agkeck-iivi/internet_radio_v3/components/pcm5122_board/pcm5122_driver.h

#ifndef __PCM5122_H__
#define __PCM5122_H__

#include "audio_hal.h"
#include "driver/i2c.h"
#include "esp_types.h"

#ifdef __cplusplus
extern "C" {
#endif

#define PCM5122_ADDR 0x98 // 8-bit Write Address (7-bit 0x4C << 1)

// Selected PCM5122 Registers
#define PCM5122_PAGE 0x00
#define PCM5122_RESET 0x01
#define PCM5122_STANDBY 0x02
#define PCM5122_MUTE 0x03
#define PCM5122_PLL_EN 0x04
#define PCM5122_PLL_REF 0x0D
#define PCM5122_DAC_CLK_SRC 0x0E
#define PCM5122_ERROR_DETECT 0x25
#define PCM5122_I2S_CONFIG 0x28
#define PCM5122_VOL_L 0x3D
#define PCM5122_VOL_R 0x3E
#define PCM5122_DIGITAL_VOL_CTRL 0x3C
#define PCM5122_DIGITAL_VOL_RAMP 0x3F
#define PCM5122_AUTO_MUTE 0x41
#define PCM5122_ANALOG_GAIN_L 0x6C
#define PCM5122_ANALOG_GAIN_R 0x6D
#define PCM5122_POWER_STATE 0x76

#define PCM5122_PLL_REF_BCK 0x10
#define PCM5122_DAC_CLK_PLL 0x10

// Digital Volume Ramp Control (Reg 63)
// Frequency: 00=every sample, 01=2nd, 10=4th, 11=8th
// Step: 00=0.5dB, 01=1dB, 10=2dB, 11=4dB
#define PCM5122_RAMP_FREQ_1FS 0x00
#define PCM5122_RAMP_FREQ_2FS 0x01
#define PCM5122_RAMP_FREQ_4FS 0x02
#define PCM5122_RAMP_FREQ_8FS 0x03

#define PCM5122_RAMP_STEP_0_5DB 0x00
#define PCM5122_RAMP_STEP_1DB 0x01
#define PCM5122_RAMP_STEP_2DB 0x02
#define PCM5122_RAMP_STEP_4DB 0x03

// Macros to build the Reg 63 value
#define PCM5122_RAMP_UP_CONFIG(freq, step) (((freq) << 6) | ((step) << 4))
#define PCM5122_RAMP_DN_CONFIG(freq, step) (((freq) << 2) | ((step) << 0))

esp_err_t pcm5122_init(audio_hal_codec_config_t *cfg);
esp_err_t pcm5122_deinit(void);

esp_err_t pcm5122_ctrl_state(audio_hal_codec_mode_t mode,
                             audio_hal_ctrl_t ctrl_state);
esp_err_t pcm5122_config_i2s(audio_hal_codec_mode_t mode,
                             audio_hal_codec_i2s_iface_t *iface);

esp_err_t pcm5122_set_voice_volume(int volume);
esp_err_t pcm5122_get_voice_volume(int *volume);
esp_err_t pcm5122_apply_analog_attenuation(void);

esp_err_t pcm5122_set_mute(bool enable);
esp_err_t pcm5122_get_mute(bool *mute);

esp_err_t pcm5122_set_ramp_rate(uint8_t config_val);

esp_err_t pcm5122_pa_power(bool enable);

#ifdef __cplusplus
}
#endif

#endif //__PCM5122_H__
