agkeck-iivi/internet_radio_v3/main/audio_pipeline_manager.c

#include "audio_pipeline_manager.h"
#include "aac_decoder.h"
#include "app_config.h"
#include "audio_common.h"
#include "audio_event_iface.h"
#include "board.h" // For CONFIG_ESP32_C3_LYRA_V2_BOARD and I2S_STREAM_PDM_TX_CFG_DEFAULT
#include "driver/gpio.h"
#include "esp_log.h"
#include "esp_sleep.h"
#include "esp_task_wdt.h"
#include "flac_decoder.h"
#include "http_stream.h"
#include "i2s_stream.h"
#include "internet_radio_adf.h"
#include "ir_remote.h"
#include "lvgl_ssd1306_setup.h"
#include "mp3_decoder.h"
#include "ogg_decoder.h"
#include "sdkconfig.h"
#include <string.h>

extern audio_pipeline_components_t audio_pipeline_components;
extern volatile bool g_is_pipeline_running;

static const char *TAG = "AUDIO_PIPELINE_MGR";
volatile uint64_t g_bytes_read = 0;

const char *codec_type_to_string(codec_type_t codec) {
  switch (codec) {
  case CODEC_TYPE_MP3:
    return "MP3";
  case CODEC_TYPE_AAC:
    return "AAC";
  case CODEC_TYPE_OGG:
    return "OGG";
  case CODEC_TYPE_FLAC:
    return "FLAC";
  default:
    return "Unknown Codec";
  }
}

void delayed_audio_on_task(void *pvParameters) {
  vTaskDelay(pdMS_TO_TICKS(200));
  ESP_ERROR_CHECK(ir_remote_turn_audio_on());
  vTaskDelete(NULL);
}

static int _http_stream_event_handle(http_stream_event_msg_t *msg) {
  switch (msg->event_id) {
  case HTTP_STREAM_RESOLVE_ALL_TRACKS:
    return ESP_OK;

  case HTTP_STREAM_FINISH_TRACK:
    return http_stream_next_track(msg->el);

  case HTTP_STREAM_FINISH_PLAYLIST:
    return http_stream_fetch_again(msg->el);

  case HTTP_STREAM_ON_RESPONSE:
    // This is called for each chunk of data received
    g_bytes_read += msg->buffer_len;
    // You could log it here, but it will be very verbose.
    // ESP_LOGI(TAG, "Bytes read: %llu", g_bytes_read);
    return ESP_OK;
  default:
    return ESP_OK;
  }
}

static esp_err_t codec_event_cb(audio_element_handle_t el,
                                audio_event_iface_msg_t *msg, void *ctx) {
  ESP_LOGI(TAG, "Codec event callback triggered for element: %s, command: %d",
           audio_element_get_tag(el), msg->cmd);
  if (msg->source_type == AUDIO_ELEMENT_TYPE_ELEMENT &&
      msg->source == (void *)el) {
    if (msg->cmd == AEL_MSG_CMD_REPORT_MUSIC_INFO) {
      audio_element_info_t music_info = {0};
      audio_element_getinfo(el, &music_info);
      ESP_LOGI(TAG,
               "[ * ] Callback: Receive music info from codec decoder, "
               "sample_rate=%d, bits=%d, ch=%d",
               music_info.sample_rates, music_info.bits, music_info.channels);
      ESP_ERROR_CHECK(i2s_stream_set_clk(
          audio_pipeline_components.i2s_stream_writer, music_info.sample_rates,
          music_info.bits, music_info.channels));

      extern bool get_mute_state(void);
      if (g_runtime_config.ir_protocol != IR_PROTOCOL_NONE) {
        ESP_LOGI(TAG, "Audio stream active. Ensuring Bose Audio is ON.");
        ir_remote_turn_audio_on();
        // send another ir command after a delay
        xTaskCreate(delayed_audio_on_task, "delayed_audio_on_task", 3*1024, NULL,
                    tskIDLE_PRIORITY + 1, NULL);
      }
    }
  }
  return ESP_OK;
}
esp_err_t create_audio_pipeline(audio_pipeline_components_t *components,
                                codec_type_t codec_type, const char *uri) {

  if (components == NULL) {
    ESP_LOGE(TAG, "audio_pipeline_components_t pointer is NULL");
    return ESP_ERR_INVALID_ARG;
  }
  if (uri == NULL) {
    ESP_LOGE(TAG, "URI is NULL");
    return ESP_ERR_INVALID_ARG;
  }
  // board works here
  esp_err_t ret = ESP_OK;

  ESP_LOGI(TAG, "Creating audio pipeline for codec type: %s with URI: %s",
           codec_type_to_string(codec_type), uri);

  // Save current state for recreation after wakeup
  components->current_codec = codec_type;
  strncpy(components->current_uri, uri, sizeof(components->current_uri) - 1);
  components->current_uri[sizeof(components->current_uri) - 1] = '\0';

  audio_pipeline_cfg_t pipeline_cfg = DEFAULT_AUDIO_PIPELINE_CONFIG();
  //   pipeline_cfg.rb_size = 64 * 1024;
  components->pipeline = audio_pipeline_init(&pipeline_cfg);
  if (components->pipeline == NULL) {
    ESP_LOGE(TAG, "Failed to initialize audio pipeline");
    ret = ESP_FAIL;
    goto cleanup;
  }

  http_stream_cfg_t http_cfg = HTTP_STREAM_CFG_DEFAULT();
  http_cfg.event_handle = _http_stream_event_handle;
  http_cfg.type = AUDIO_STREAM_READER;
  http_cfg.enable_playlist_parser = true;
  components->http_stream_reader = http_stream_init(&http_cfg);
  if (components->http_stream_reader == NULL) {
    ESP_LOGE(TAG, "Failed to initialize HTTP stream reader");
    ret = ESP_FAIL;
    goto cleanup;
  }
  // // custom reader to skip junk data before mp3 frames in shoutcast streams
  // // this should be switchable.
  // audio_element_set_read_cb(components->http_stream_reader, custom_read,
  // NULL);

#if defined CONFIG_ESP32_C3_LYRA_V2_BOARD
  i2s_stream_cfg_t i2s_cfg = I2S_STREAM_PDM_TX_CFG_DEFAULT();
#else
  i2s_stream_cfg_t i2s_cfg = I2S_STREAM_CFG_DEFAULT();
#endif
  i2s_cfg.type = AUDIO_STREAM_WRITER;
  components->i2s_stream_writer = i2s_stream_init(&i2s_cfg);
  if (components->i2s_stream_writer == NULL) {
    ESP_LOGE(TAG, "Failed to initialize I2S stream writer");
    ret = ESP_FAIL;
    goto cleanup;
  }

  switch (codec_type) {
  case CODEC_TYPE_AAC:
    ESP_LOGD(TAG, "Creating AAC decoder");
    aac_decoder_cfg_t aac_cfg = DEFAULT_AAC_DECODER_CONFIG();
    aac_cfg.task_core = 1; // unacceptable clicking a popping on KXLU
    aac_cfg.plus_enable = true;
    components->codec_decoder = aac_decoder_init(&aac_cfg);
    break;
  case CODEC_TYPE_MP3:
    ESP_LOGD(TAG, "Creating MP3 decoder");
    mp3_decoder_cfg_t mp3_cfg = DEFAULT_MP3_DECODER_CONFIG();
    mp3_cfg.task_core = 1;
    components->codec_decoder = mp3_decoder_init(&mp3_cfg);
    break;
  case CODEC_TYPE_OGG:
    ESP_LOGD(TAG, "Creating OGG decoder");
    ogg_decoder_cfg_t ogg_cfg = DEFAULT_OGG_DECODER_CONFIG();
    ogg_cfg.task_core = 1;
    components->codec_decoder = ogg_decoder_init(&ogg_cfg);
    break;
  case CODEC_TYPE_FLAC:
    ESP_LOGD(TAG, "Creating FLAC decoder");
    flac_decoder_cfg_t flac_cfg = DEFAULT_FLAC_DECODER_CONFIG();
    flac_cfg.task_core = 1;
    components->codec_decoder = flac_decoder_init(&flac_cfg);
    break;
  default:
    ESP_LOGE(TAG, "Unsupported codec type: %d", codec_type);
    ret = ESP_ERR_INVALID_ARG;
    goto cleanup;
  }
  if (components->codec_decoder == NULL) {
    ESP_LOGE(TAG, "Failed to initialize %s decoder",
             codec_type_to_string(codec_type));
    ret = ESP_FAIL;
    goto cleanup;
  }
  // codec callback filters for music info (sample rate, bits, channels) and
  // sets i2s stream clock
  audio_element_set_event_callback(components->codec_decoder, codec_event_cb,
                                   NULL);

  if (audio_pipeline_register(components->pipeline,
                              components->http_stream_reader,
                              "http") != ESP_OK ||
      audio_pipeline_register(components->pipeline, components->codec_decoder,
                              "codec") != ESP_OK ||
      audio_pipeline_register(components->pipeline,
                              components->i2s_stream_writer, "i2s") != ESP_OK) {
    ESP_LOGE(TAG, "Failed to register audio elements to pipeline");
    ret = ESP_FAIL;
    goto cleanup;
  }

  const char *link_tag[3] = {"http", "codec", "i2s"};
  if (audio_pipeline_link(components->pipeline, &link_tag[0], 3) != ESP_OK) {
    ESP_LOGE(TAG, "Failed to link pipeline elements: http->%s->i2s",
             codec_type_to_string(codec_type));
    ret = ESP_FAIL;
    goto cleanup;
  }

  if (audio_element_set_uri(components->http_stream_reader, uri) != ESP_OK) {
    ESP_LOGE(TAG, "Failed to set URI for http_stream_reader");
    ret = ESP_FAIL;
    goto cleanup;
  }

  ESP_LOGI(TAG, "Audio pipeline with %s codec created successfully",
           codec_type_to_string(codec_type));
  return ESP_OK;

cleanup:
  ESP_LOGE(
      TAG,
      "Cleaning up audio pipeline components due to error during creation");
  if (components->http_stream_reader) {
    audio_element_deinit(components->http_stream_reader);
    components->http_stream_reader = NULL;
  }
  if (components->codec_decoder) {
    audio_element_deinit(components->codec_decoder);
    components->codec_decoder = NULL;
  }
  if (components->i2s_stream_writer) {
    audio_element_deinit(components->i2s_stream_writer);
    components->i2s_stream_writer = NULL;
  }
  if (components->pipeline) {
    audio_pipeline_deinit(components->pipeline);
    components->pipeline = NULL;
  }
  return ret;
}

esp_err_t destroy_audio_pipeline(audio_pipeline_components_t *components) {
  if (components == NULL) {
    ESP_LOGE(TAG, "audio_pipeline_components_t pointer is NULL for destroy");
    return ESP_ERR_INVALID_ARG;
  }

  ESP_LOGI(TAG, "Destroying audio pipeline");

  if (components->pipeline) {
    audio_pipeline_stop(components->pipeline);
    audio_pipeline_wait_for_stop(components->pipeline);
    audio_pipeline_terminate(components->pipeline);
    audio_pipeline_deinit(components->pipeline); // deinits all elements
    components->pipeline = NULL;
  }
  components->http_stream_reader = NULL;
  components->codec_decoder = NULL;
  components->i2s_stream_writer = NULL;

  ESP_LOGI(TAG, "Audio pipeline destroyed successfully");
  return ESP_OK;
}

esp_err_t audio_pipeline_manager_sleep(audio_pipeline_components_t *components,
                                       int wakeup_gpio1, int wakeup_gpio2,
                                       uint64_t timer_wakeup_us) {
  // timer_wakeup_us is the duration for light sleep before potential deep sleep
  if (components == NULL || components->pipeline == NULL) {
    return ESP_ERR_INVALID_ARG;
  }

  ESP_LOGI(TAG, "Preparing pipeline for light sleep...");

  // Fully destroy the pipeline to clear any stale SSL/TCP state
  g_is_pipeline_running = false;
  destroy_audio_pipeline(components);

  ESP_LOGI(TAG, "Configuring wakeup on GPIO %d and %d (LOW level)",
           wakeup_gpio1, wakeup_gpio2);
  // 6. Configure hardware wakeup
  esp_err_t err = gpio_wakeup_enable(wakeup_gpio1, GPIO_INTR_LOW_LEVEL);
  if (err != ESP_OK) {
    ESP_LOGE(TAG, "Failed to enable GPIO wakeup 1: %d", err);
    return err;
  }
  if (wakeup_gpio2 >= 0) {
    err = gpio_wakeup_enable(wakeup_gpio2, GPIO_INTR_LOW_LEVEL);
    if (err != ESP_OK) {
      ESP_LOGE(TAG, "Failed to enable GPIO wakeup 2: %d", err);
      return err;
    }
  }
  // 7. Enable GPIO as wakeup source
  err = esp_sleep_enable_gpio_wakeup();
  if (err != ESP_OK) {
    ESP_LOGE(TAG, "Failed to enable sleep GPIO wakeup: %d", err);
    return err;
  }

  if (timer_wakeup_us > 0) {
    ESP_LOGI(TAG, "Enabling timer wakeup for %llu us", timer_wakeup_us);
    err = esp_sleep_enable_timer_wakeup(timer_wakeup_us);
    if (err != ESP_OK) {
      ESP_LOGE(TAG, "Failed to enable timer wakeup: %d", err);
      return err;
    }
  }

  ESP_LOGI(TAG, "Entering light sleep...");
  // 8. Enter low-power state
  esp_task_wdt_deinit();
  lvgl_ssd1306_sleep();

  if (g_runtime_config.ir_protocol != IR_PROTOCOL_NONE) {
    ir_remote_turn_audio_off();
  }

  esp_light_sleep_start();

  esp_task_wdt_config_t twdt_config = {
      .timeout_ms = CONFIG_ESP_TASK_WDT_TIMEOUT_S * 1000,
      .idle_core_mask = (1 << CONFIG_FREERTOS_NUMBER_OF_CORES) - 1,
      .trigger_panic = false,
  };
  esp_task_wdt_init(&twdt_config);

  ESP_LOGI(TAG, "Woke up from light sleep");
  return ESP_OK;
}

esp_err_t audio_pipeline_manager_wakeup(audio_pipeline_components_t *components,
                                        audio_event_iface_handle_t evt) {
  if (components == NULL) {
    return ESP_ERR_INVALID_ARG;
  }

  ESP_LOGI(TAG, "Recreating audio pipeline after wakeup");

  // Recreate the pipeline from scratch
  esp_err_t ret = create_audio_pipeline(components, components->current_codec,
                                        components->current_uri);
  if (ret != ESP_OK) {
    ESP_LOGE(TAG, "Failed to recreate pipeline after wakeup: %d", ret);
    return ret;
  }

  // Link event listener if provided
  if (evt) {
    audio_pipeline_set_listener(components->pipeline, evt);
  }

  // Re-run the pipeline
  reset_throughput_history();
  ret = audio_pipeline_run(components->pipeline);
  if (ret == ESP_OK) {
    g_is_pipeline_running = true;
  }
  return ret;
}
