agkeck-iivi/internet_radio_v3/main/lvgl_ssd1306_setup.c

#include "driver/spi_master.h"
#include "esp_err.h"
#include "esp_lcd_panel_io.h"
#include "esp_lcd_panel_ops.h"
#include "esp_log.h"
#include "esp_timer.h"
#include "freertos/FreeRTOS.h"
#include "freertos/task.h"
#include "lvgl.h"
#include <sys/lock.h>
#include <sys/param.h>
#include <unistd.h>

#include "esp_lcd_panel_vendor.h"
#include "screens.h"

static lv_display_t *g_display = NULL;

static const char *TAG = "init_lvgl_ssd1306";

// pin, geometry, and lvgl parameter configurations.
#include "gpio_assignments.h"
#define LCD_PIXEL_CLOCK_HZ (4 * 1000 * 1000)
#define LCD_HOST SPI2_HOST
#define PIN_NUM_SCLK DISPLAY_SPI_SCLK_GPIO
#define PIN_NUM_MOSI DISPLAY_SPI_MOSI_GPIO
#define PIN_NUM_RST DISPLAY_SPI_RST_GPIO
#define PIN_NUM_DC DISPLAY_SPI_DC_GPIO
#define PIN_NUM_CS DISPLAY_SPI_CS_GPIO

// The pixel number in horizontal and vertical
#define LCD_H_RES 128
#define LCD_V_RES 64
// Bit number used to represent command and parameter
#define LCD_CMD_BITS 8
#define LCD_PARAM_BITS 8

#define LVGL_TICK_PERIOD_MS 5
#define LVGL_TASK_STACK_SIZE (8 * 1024)
#define LVGL_TASK_PRIORITY 2
#define LVGL_PALETTE_SIZE 8
#define LVGL_TASK_MAX_DELAY_MS 100
#define LVGL_TASK_MIN_DELAY_MS 1000 / CONFIG_FREERTOS_HZ

// To use LV_COLOR_FORMAT_I1, we need an extra buffer to hold the converted data
static uint8_t oled_buffer[LCD_H_RES * LCD_V_RES / 8];
// LVGL library is not thread-safe, this example will call LVGL APIs from
// different tasks, so use a mutex to protect it
static _lock_t lvgl_api_lock;

// extern void radio_home_screen_create(lv_disp_t* disp);

static bool notify_lvgl_flush_ready(esp_lcd_panel_io_handle_t io_panel,
                                    esp_lcd_panel_io_event_data_t *edata,
                                    void *user_ctx) {
  lv_display_t *disp = (lv_display_t *)user_ctx;
  lv_display_flush_ready(disp);
  return false;
}

static void lvgl_flush_cb(lv_display_t *disp, const lv_area_t *area,
                          uint8_t *px_map) {
  esp_lcd_panel_handle_t panel_handle = lv_display_get_user_data(disp);

  // This is necessary because LVGL reserves 2 x 4 bytes in the buffer, as these
  // are assumed to be used as a palette. Skip the palette here More information
  // about the monochrome, please refer to
  // https://docs.lvgl.io/9.2/porting/display.html#monochrome-displays
  px_map += LVGL_PALETTE_SIZE;

  uint16_t hor_res = lv_display_get_physical_horizontal_resolution(disp);
  int x1 = area->x1;
  int x2 = area->x2;
  int y1 = area->y1;
  int y2 = area->y2;

  for (int y = y1; y <= y2; y++) {
    for (int x = x1; x <= x2; x++) {
      /* The order of bits is MSB first
                  MSB           LSB
         bits      7 6 5 4 3 2 1 0
         pixels    0 1 2 3 4 5 6 7
                  Left         Right
      */
      bool chroma_color =
          (px_map[(hor_res >> 3) * y + (x >> 3)] & 1 << (7 - x % 8));

      /* Write to the buffer as required for the display.
       * It writes only 1-bit for monochrome displays mapped vertically.*/
      uint8_t *buf = oled_buffer + hor_res * (y >> 3) + (x);
      if (chroma_color) {
        (*buf) &= ~(1 << (y % 8));
      } else {
        (*buf) |= (1 << (y % 8));
      }
    }
  }
  // pass the draw buffer to the driver
  esp_lcd_panel_draw_bitmap(panel_handle, x1, y1, x2 + 1, y2 + 1, oled_buffer);
}

static void increase_lvgl_tick(void *arg) {
  /* Tell LVGL how many milliseconds has elapsed */
  lv_tick_inc(LVGL_TICK_PERIOD_MS);
}

static void lvgl_port_task(void *arg) {
  ESP_LOGI(TAG, "Starting LVGL task");
  uint32_t time_till_next_ms = 0;
  while (1) {
    _lock_acquire(&lvgl_api_lock);
    process_ui_updates();
    time_till_next_ms = lv_timer_handler();
    _lock_release(&lvgl_api_lock);
    // in case of triggering a task watch dog time out
    time_till_next_ms = MAX(time_till_next_ms, LVGL_TASK_MIN_DELAY_MS);
    // in case of lvgl display not ready yet
    time_till_next_ms = MIN(time_till_next_ms, LVGL_TASK_MAX_DELAY_MS);
    usleep(1000 * time_till_next_ms);
  }
}

lv_display_t *lvgl_ssd1306_setup(void) {
  ESP_LOGI(TAG, "Initialize SPI bus");
  spi_bus_config_t buscfg = {
      .sclk_io_num = PIN_NUM_SCLK,
      .mosi_io_num = PIN_NUM_MOSI,
      .miso_io_num = -1,
      .quadwp_io_num = -1,
      .quadhd_io_num = -1,
      .max_transfer_sz = LCD_H_RES * LCD_V_RES / 8,
  };
  ESP_ERROR_CHECK(spi_bus_initialize(LCD_HOST, &buscfg, SPI_DMA_CH_AUTO));

  ESP_LOGI(TAG, "Install panel IO");
  esp_lcd_panel_io_handle_t io_handle = NULL;
  esp_lcd_panel_io_spi_config_t io_config = {
      .dc_gpio_num = PIN_NUM_DC,
      .cs_gpio_num = PIN_NUM_CS,
      .pclk_hz = LCD_PIXEL_CLOCK_HZ,
      .lcd_cmd_bits = LCD_CMD_BITS,
      .lcd_param_bits = LCD_PARAM_BITS,
      .spi_mode = 0,
      .trans_queue_depth = 10,
      .on_color_trans_done = notify_lvgl_flush_ready,
      .user_ctx = NULL, // Will be set later
      .flags =
          {
              .dc_low_on_param = 1,
          } // added by agk
  };
  // Attach the LCD to the SPI bus
  ESP_ERROR_CHECK(esp_lcd_new_panel_io_spi((esp_lcd_spi_bus_handle_t)LCD_HOST,
                                           &io_config, &io_handle));

  ESP_LOGI(TAG, "Install SSD1306 panel driver");
  esp_lcd_panel_handle_t panel_handle = NULL;

  esp_lcd_panel_dev_config_t panel_config = {
      .bits_per_pixel = 1,
      .reset_gpio_num = PIN_NUM_RST,
  };
  esp_lcd_panel_ssd1306_config_t ssd1306_config = {
      .height = LCD_V_RES,
  };
  panel_config.vendor_config = &ssd1306_config;
  ESP_ERROR_CHECK(
      esp_lcd_new_panel_ssd1306(io_handle, &panel_config, &panel_handle));

  // neither of these allowed me to change the orientation.
  // ESP_ERROR_CHECK(esp_lcd_panel_mirror(panel_handle, 1, 1));
  // esp_lcd_panel_swap_xy(panel_handle, 0);

  ESP_ERROR_CHECK(esp_lcd_panel_reset(panel_handle));
  ESP_ERROR_CHECK(esp_lcd_panel_init(panel_handle));
  ESP_ERROR_CHECK(esp_lcd_panel_mirror(
      panel_handle, 1, 1)); // this swaps top and bottom of display
  ESP_ERROR_CHECK(esp_lcd_panel_disp_on_off(panel_handle, true));

  ESP_LOGI(TAG, "Initialize LVGL");
  lv_init();
  // create a lvgl display
  lv_display_t *display = lv_display_create(LCD_H_RES, LCD_V_RES);
  // associate the i2c panel handle to the display
  lv_display_set_user_data(display, panel_handle);
  io_config.user_ctx = display; // Set user context for the callback
  // create draw buffer
  void *buf = NULL;
  ESP_LOGI(TAG, "Allocate separate LVGL draw buffers");
  // LVGL reserves 2 x 4 bytes in the buffer, as these are assumed to be used as
  // a palette.
  size_t draw_buffer_sz = LCD_H_RES * LCD_V_RES / 8 + LVGL_PALETTE_SIZE;
  buf = heap_caps_calloc(1, draw_buffer_sz,
                         MALLOC_CAP_INTERNAL | MALLOC_CAP_8BIT);
  assert(buf);

  // LVGL9 suooprt new monochromatic format.
  lv_display_set_color_format(display, LV_COLOR_FORMAT_I1);
  // initialize LVGL draw buffers
  lv_display_set_buffers(display, buf, NULL, draw_buffer_sz,
                         LV_DISPLAY_RENDER_MODE_FULL);
  // set the callback which can copy the rendered image to an area of the
  // display
  lv_display_set_flush_cb(display, lvgl_flush_cb);

  ESP_LOGI(
      TAG,
      "Register io panel event callback for LVGL flush ready notification");
  const esp_lcd_panel_io_callbacks_t cbs = {
      .on_color_trans_done = notify_lvgl_flush_ready,
  };
  /* Register done callback */
  esp_lcd_panel_io_register_event_callbacks(io_handle, &cbs, display);

  ESP_LOGI(TAG, "Use esp_timer as LVGL tick timer");
  const esp_timer_create_args_t lvgl_tick_timer_args = {
      .callback = &increase_lvgl_tick, .name = "lvgl_tick"};
  esp_timer_handle_t lvgl_tick_timer = NULL;
  ESP_ERROR_CHECK(esp_timer_create(&lvgl_tick_timer_args, &lvgl_tick_timer));
  ESP_ERROR_CHECK(
      esp_timer_start_periodic(lvgl_tick_timer, LVGL_TICK_PERIOD_MS * 1000));

  ESP_LOGI(TAG, "Create LVGL task");
  xTaskCreate(lvgl_port_task, "LVGL", LVGL_TASK_STACK_SIZE, NULL,
              LVGL_TASK_PRIORITY, NULL);
  g_display = display;
  return display;
}

void lvgl_ssd1306_wakeup(void) {
  if (g_display == NULL)
    return;
  esp_lcd_panel_handle_t panel_handle = lv_display_get_user_data(g_display);
  if (panel_handle) {
    ESP_LOGI(TAG, "Re-initializing SSD1306 panel after wakeup");
    _lock_acquire(&lvgl_api_lock);
    // Reset and init to restore state after pin isolation/power gating
    esp_lcd_panel_reset(panel_handle);
    esp_lcd_panel_init(panel_handle);
    esp_lcd_panel_mirror(panel_handle, 1, 1);
    esp_lcd_panel_disp_on_off(panel_handle, true);
    _lock_release(&lvgl_api_lock);
  }
}

void lvgl_ssd1306_sleep(void) {
  if (g_display == NULL)
    return;
  esp_lcd_panel_handle_t panel_handle = lv_display_get_user_data(g_display);
  if (panel_handle) {
    ESP_LOGI(TAG, "Turning off SSD1306 panel for sleep");
    _lock_acquire(&lvgl_api_lock);
    esp_lcd_panel_disp_on_off(panel_handle, false);
    _lock_release(&lvgl_api_lock);
  }
}
