agkeck-iivi/internet_radio_v3/components/pcm5122_board/board.c

#include "board.h"
#include "audio_mem.h"
#include "esp_log.h"
#include "pcm5122_driver.h"

static const char *TAG = "PCM5122_BOARD";

static audio_board_handle_t board_handle = 0;

audio_board_handle_t audio_board_init(void) {
  if (board_handle) {
    ESP_LOGW(TAG, "The board has already been initialized!");
    return board_handle;
  }
  board_handle =
      (audio_board_handle_t)audio_calloc(1, sizeof(struct audio_board_handle));
  AUDIO_MEM_CHECK(TAG, board_handle, return NULL);
  board_handle->audio_hal = audio_board_codec_init();
  return board_handle;
}

audio_hal_handle_t audio_board_codec_init(void) {
  audio_hal_codec_config_t audio_codec_cfg = AUDIO_CODEC_DEFAULT_CONFIG();
  audio_hal_handle_t codec_hal =
      audio_hal_init(&audio_codec_cfg, &MY_AUDIO_CODEC_PCM5122_DEFAULT_HANDLE);
  AUDIO_NULL_CHECK(TAG, codec_hal, return NULL);
  return codec_hal;
}

audio_board_handle_t audio_board_get_handle(void) { return board_handle; }

esp_err_t audio_board_deinit(audio_board_handle_t audio_board) {
  esp_err_t ret = ESP_OK;
  ret = audio_hal_deinit(audio_board->audio_hal);
  audio_free(audio_board);
  board_handle = NULL;
  return ret;
}

esp_err_t audio_board_mute(bool mute) {
  if (board_handle == NULL || board_handle->audio_hal == NULL) {
    return ESP_ERR_INVALID_STATE;
  }
  return audio_hal_set_mute(board_handle->audio_hal, mute);
}

esp_err_t audio_board_get_mute(bool *mute) {
  if (board_handle == NULL || board_handle->audio_hal == NULL) {
    return ESP_ERR_INVALID_STATE;
  }
  // We call the driver function directly as it's not in the audio_hal_func_t
  // struct
  return pcm5122_get_mute(mute);
}
