agkeck-iivi/internet_radio_v3/components/pcm5122_board/board.h

#ifndef _AUDIO_BOARD_H_
#define _AUDIO_BOARD_H_

#include "board_def.h"
#include "board_pins_config.h"

#ifdef __cplusplus
extern "C" {
#endif

typedef struct audio_board_handle *audio_board_handle_t;

struct audio_board_handle {
  audio_hal_handle_t audio_hal;
};

audio_board_handle_t audio_board_init(void);
audio_board_handle_t audio_board_get_handle(void);
esp_err_t audio_board_deinit(audio_board_handle_t audio_board);
audio_hal_handle_t audio_board_codec_init(void);
esp_err_t audio_board_mute(bool mute);
esp_err_t audio_board_get_mute(bool *mute);

#ifdef __cplusplus
}
#endif

#endif
